Makerfabs/Makerfabs-ESP32-S3-Parallel-TFT-with-Touch/example/esp-idf/lvgl9_demo/main/release/matouch-1-8-s3/assets/img_2.jpg

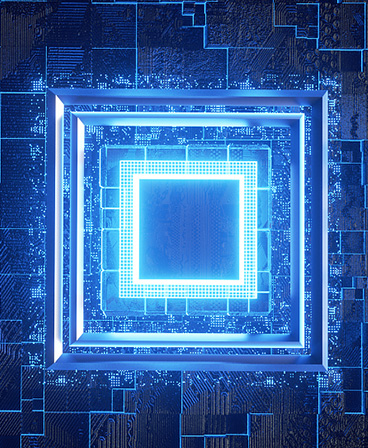
example/esp-idf/lvgl9_demo/main/release/matouch-1-8-s3/assets/img_2.jpg
