Makerfabs/Makerfabs-ESP32-S3-Parallel-TFT-with-Touch/Run LVGL On Matouch Display/ui/FT6236.cpp

#include "FT6236.h"

int readTouchReg(int reg)
{
    int data = 0;
    Wire.beginTransmission(TOUCH_I2C_ADD);
    Wire.write(reg);
    Wire.endTransmission();
    Wire.requestFrom(TOUCH_I2C_ADD, 1);
    if (Wire.available())
    {
        data = Wire.read();
    }
    return data;
}

int get_pos(int *x, int *y)
{
    int XL = 0;
    int XH = 0;
    int YL = 0;
    int YH = 0;

    XH = readTouchReg(TOUCH_REG_XH);
    if (XH >> 6 == 1)
    {
        *x = -1;
        *y = -1;
        return 0;
    }
    XL = readTouchReg(TOUCH_REG_XL);
    YH = readTouchReg(TOUCH_REG_YH);
    YL = readTouchReg(TOUCH_REG_YL);

    *x = ((XH & 0x0F) << 8) | XL;
    *y = ((YH & 0x0F) << 8) | YL;
    return 1;
}
