Makerfabs/Makerfabs-ESP32-S3-Parallel-TFT-with-Touch/Run LVGL On Matouch Display/ui/FT6236.h

#include <Wire.h>

#define TOUCH_I2C_ADD 0x38

#define TOUCH_REG_XL 0x04
#define TOUCH_REG_XH 0x03
#define TOUCH_REG_YL 0x06
#define TOUCH_REG_YH 0x05

int readTouchReg(int reg);
int get_pos(int *x, int *y);
